OpeningDesign/Stephan_Brady_Balcony/Model/source/metal+texture+pattern+5.jpg

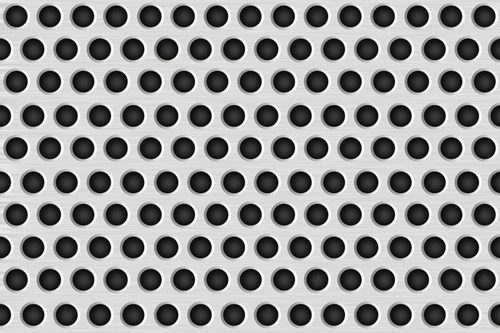
Model/source/metal+texture+pattern+5.jpg
