OpeningDesign/Stephan_Brady_Balcony/Model/source/seamless.png

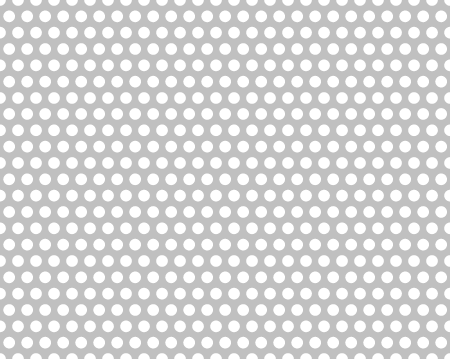
Model/source/seamless.png
