OpeningDesign/Stephan_Brady_Balcony/Structural/Pictures/20150319_081041 1.jpg

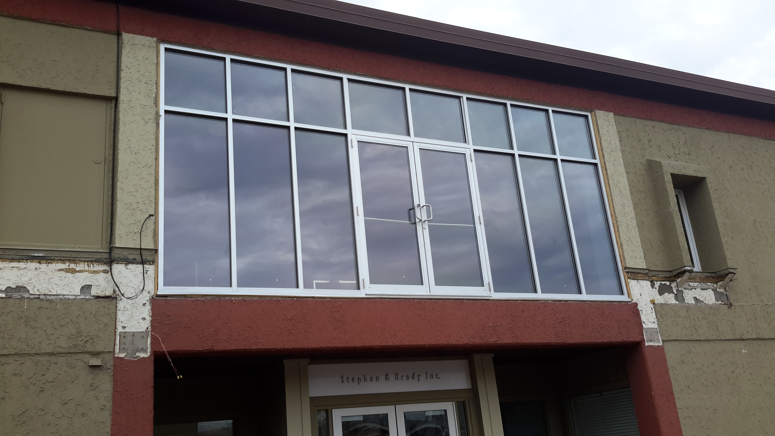
Structural/Pictures/20150319_081041 1.jpg
