OpeningDesign/Stephan_Brady_Balcony/Structural/Pictures/20150319_081100.jpg

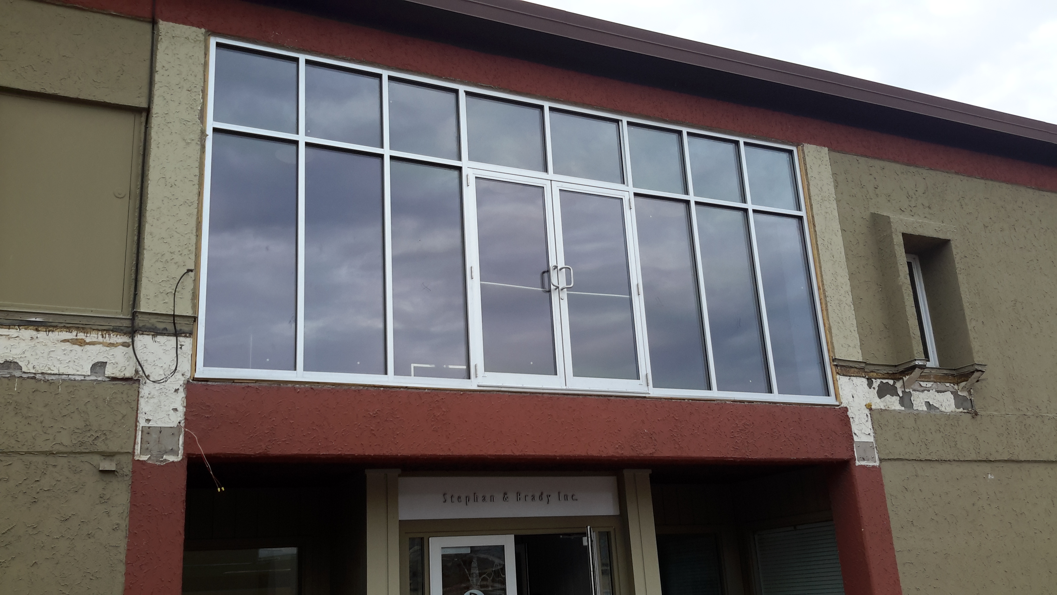
Structural/Pictures/20150319_081100.jpg
