OpeningDesign/Stephan_Brady_Balcony/Structural/Pictures/20150319_081543.jpg

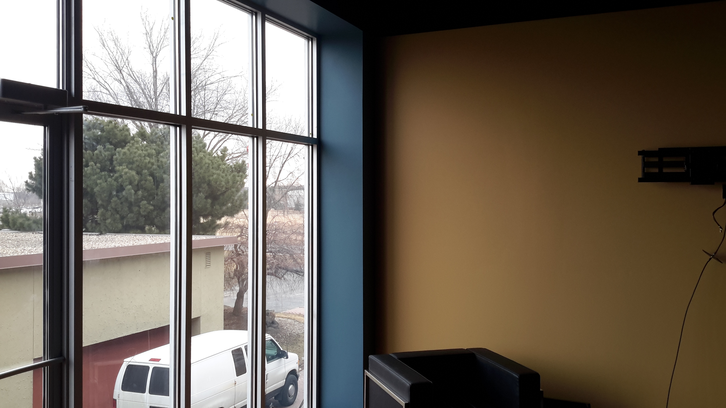
Structural/Pictures/20150319_081543.jpg
