OpeningDesign/Stephan_Brady_Balcony/Structural/Pictures/20150319_081604.jpg

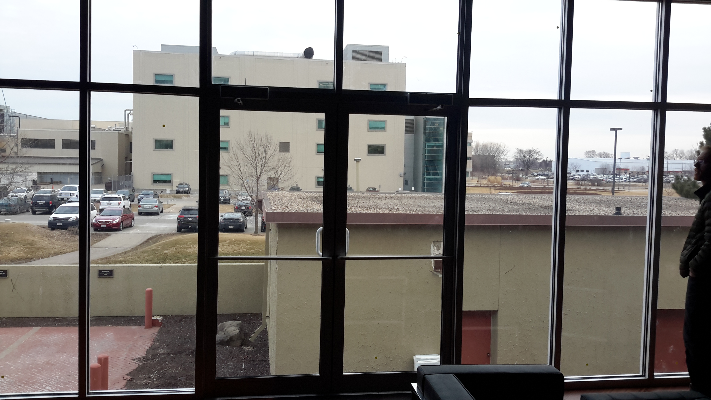
Structural/Pictures/20150319_081604.jpg
