OpeningDesign/Stephan_Brady_Balcony/Structural/Pictures/20150319_082054.jpg

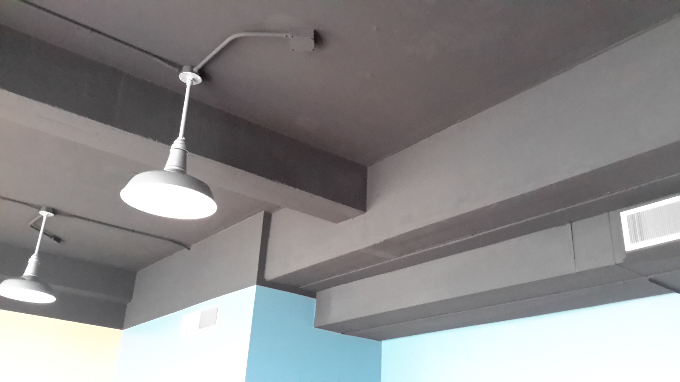
Structural/Pictures/20150319_082054.jpg
