OpeningDesign/Stephan_Brady_Balcony/Structural/Pictures/20150319_082059.jpg

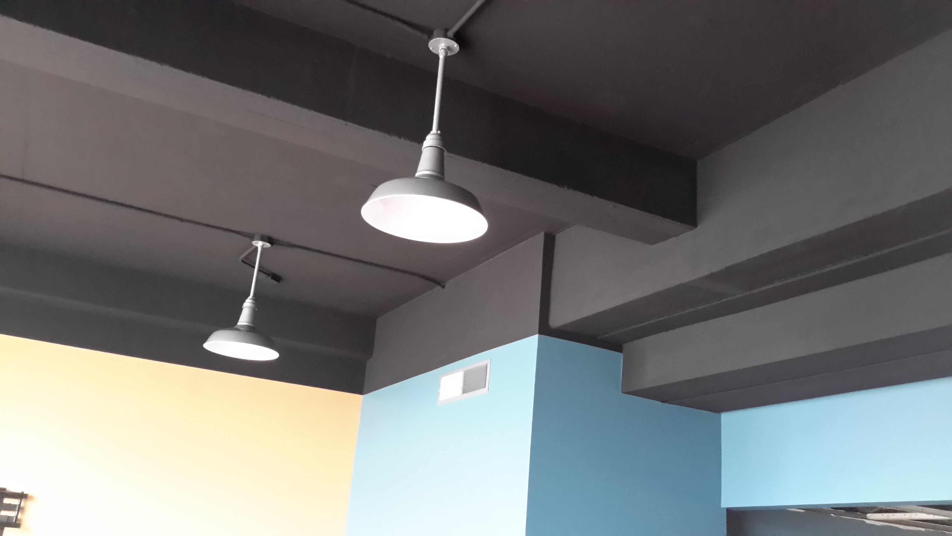
Structural/Pictures/20150319_082059.jpg
