OpeningDesign/Stephan_Brady_Balcony/Structural/Pictures/20150319_091719.jpg

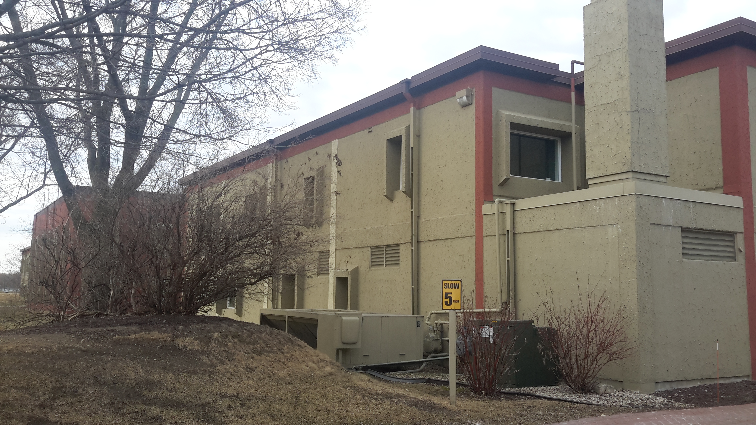
Structural/Pictures/20150319_091719.jpg
