OpeningDesign/Stephan_Brady_Balcony/Transfer/20150226 - Owner design review/SB_Balcony.rvt_2015-Feb-26_03-01-39PM-000_Perspective_-_Café_Balcony_-_Street_Approach_1.png

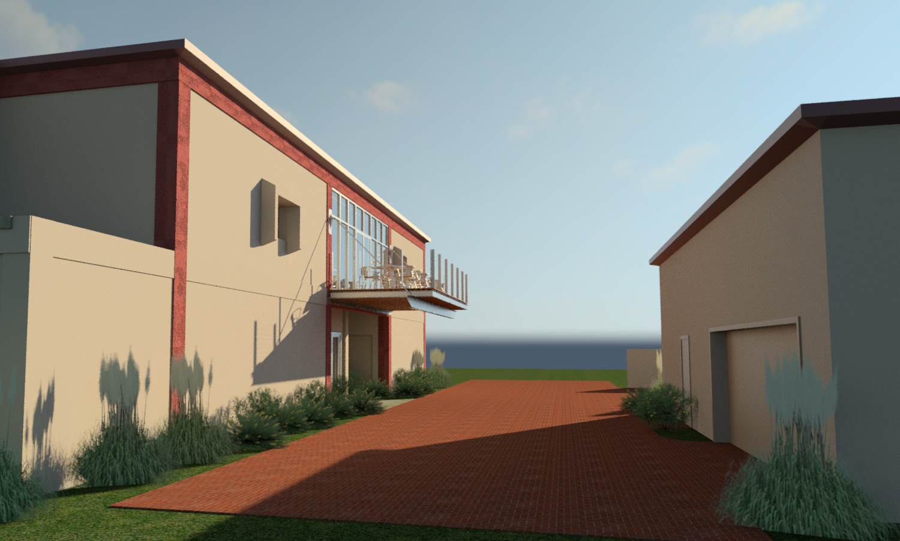
Transfer/20150226 - Owner design review/SB_Balcony.rvt_2015-Feb-26_03-01-39PM-000_Perspective_-_Café_Balcony_-_Street_Approach_1.png
