OpeningDesign/Stephan_Brady_Balcony/Transfer/20150311_ updated design/SB_Balcony.rvt_2015-Mar-11_02-54-14PM-000_Perspective_-_Café_Room.png

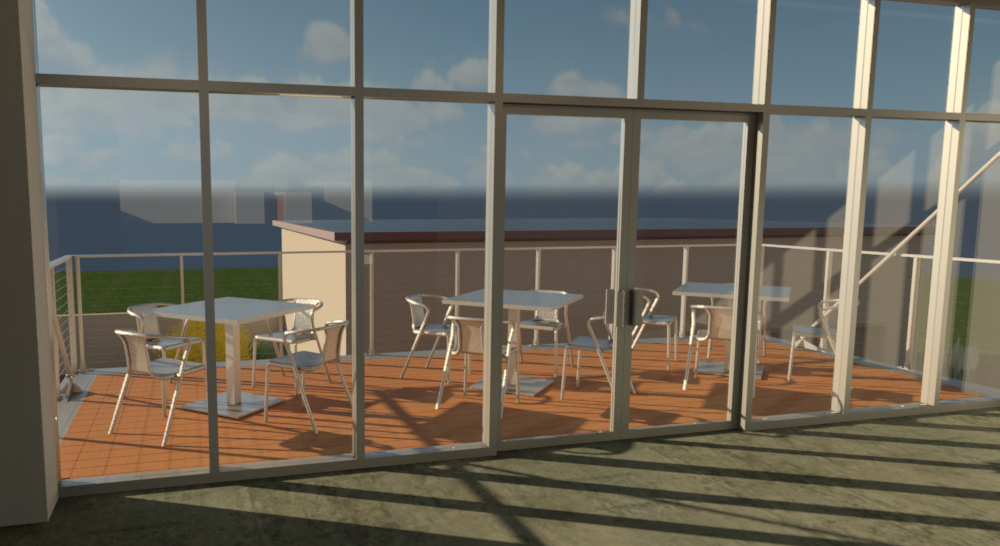
Transfer/20150311_ updated design/SB_Balcony.rvt_2015-Mar-11_02-54-14PM-000_Perspective_-_Café_Room.png
