OpeningDesign/Stephan_Brady_Balcony/Transfer/20150514 - scan of rebar in column and beam/Scanning Document.jpg

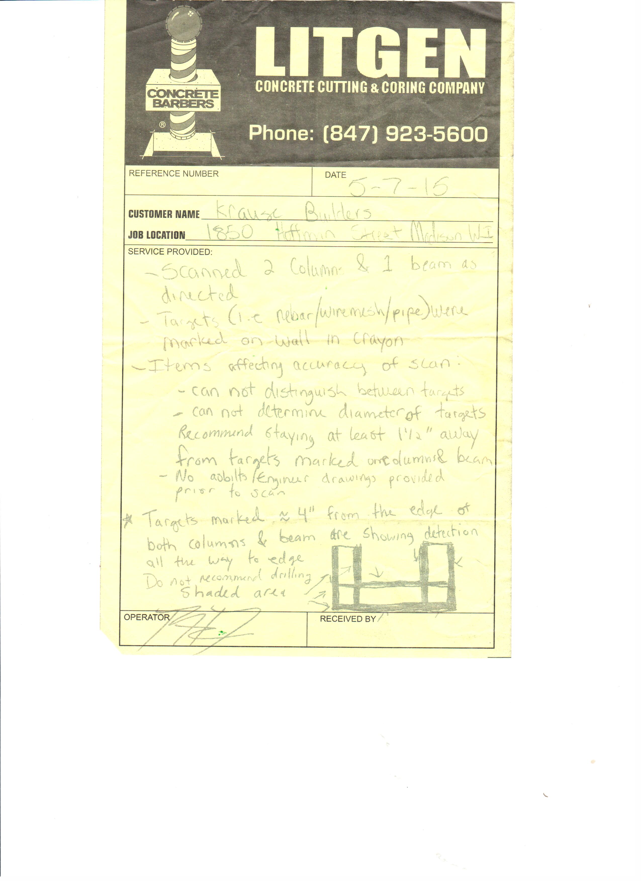
Transfer/20150514 - scan of rebar in column and beam/Scanning Document.jpg
